brayan832015/Taller_Integrador/docs/final report/Figures/making/2_fabricacion_drilling.jpeg

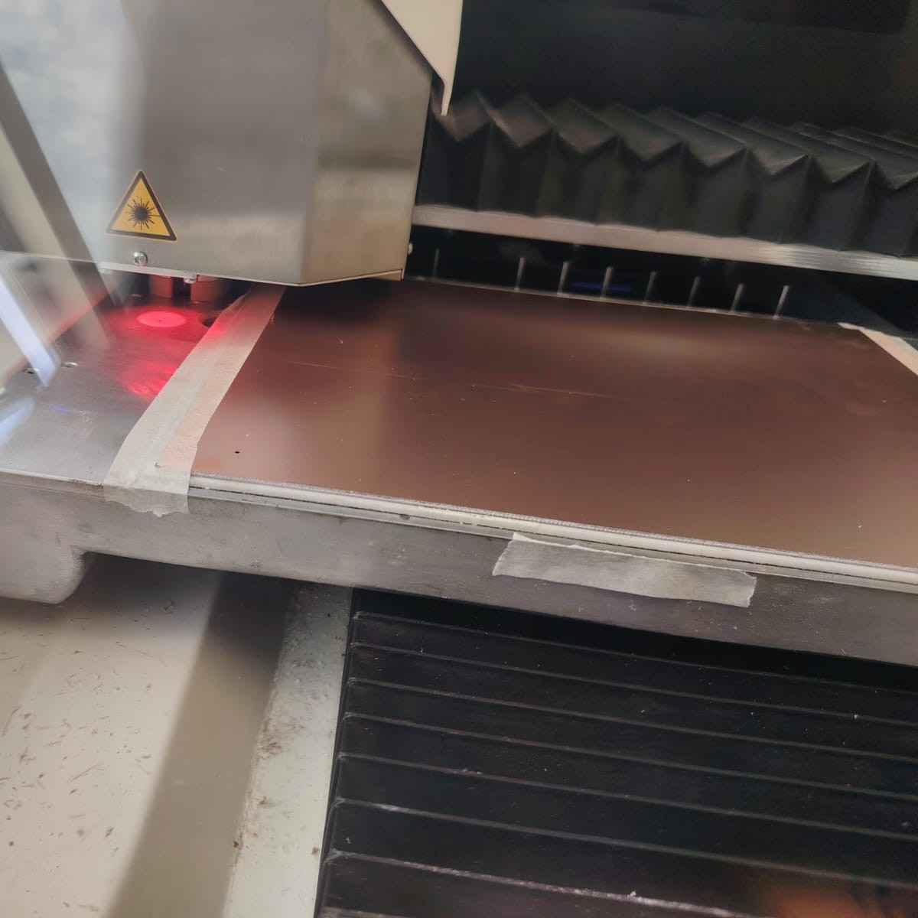
docs/final report/Figures/making/2_fabricacion_drilling.jpeg
