brayan832015/Taller_Integrador/docs/final report/Figures/making/4_fabricacion_baño.jpeg

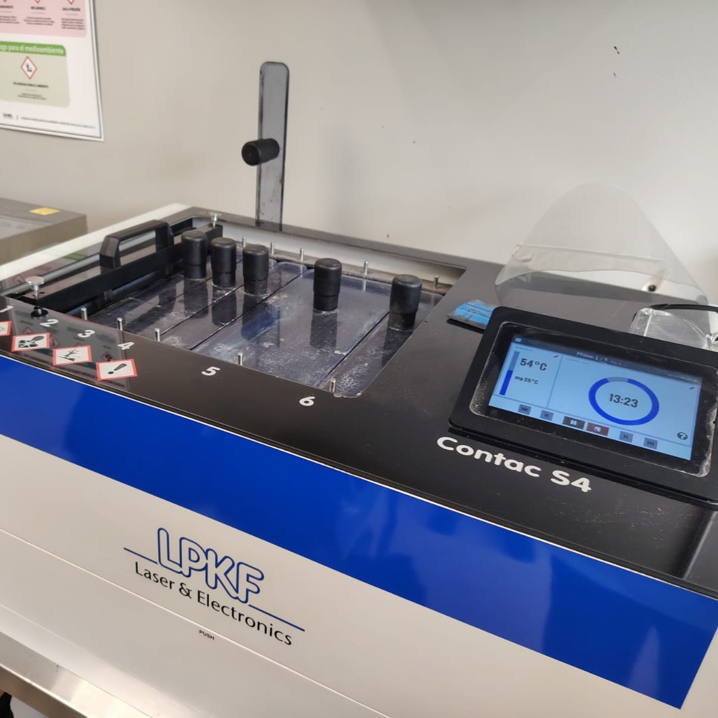
docs/final report/Figures/making/4_fabricacion_baño.jpeg
