brayan832015/Taller_Integrador/docs/final report/Figures/making/5_fabricacion_baño.jpeg

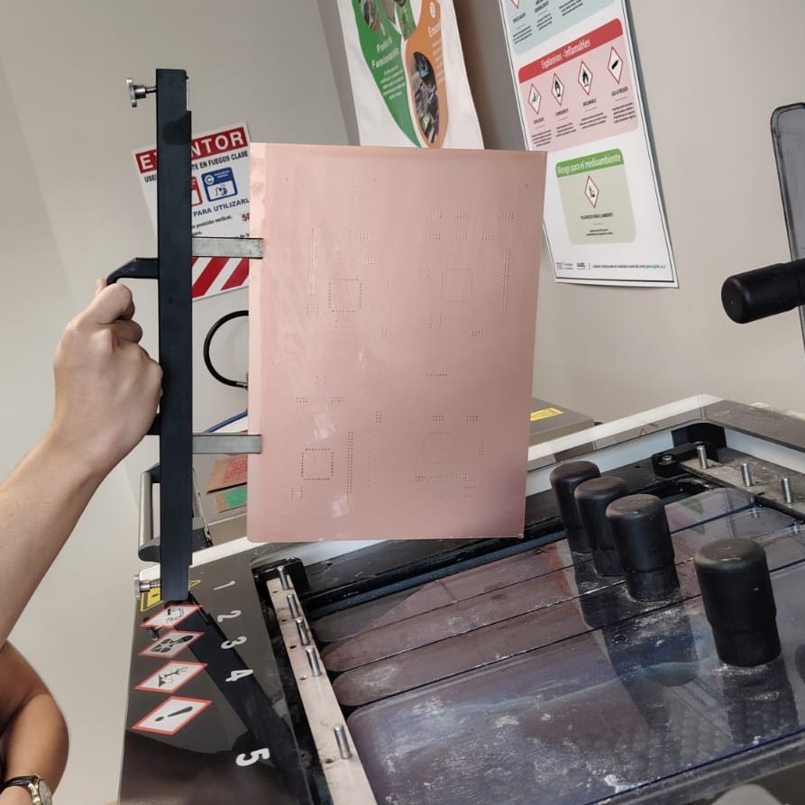
docs/final report/Figures/making/5_fabricacion_baño.jpeg
