brayan832015/Taller_Integrador/docs/final report/Figures/making/10_fabricacion_orificios_metal.jpeg

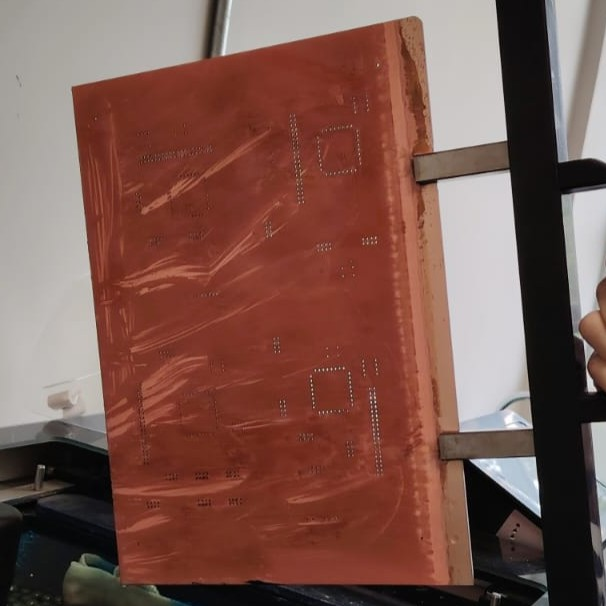
docs/final report/Figures/making/10_fabricacion_orificios_metal.jpeg
