brayan832015/Taller_Integrador/docs/final report/Figures/making/18_soldadura.jpeg

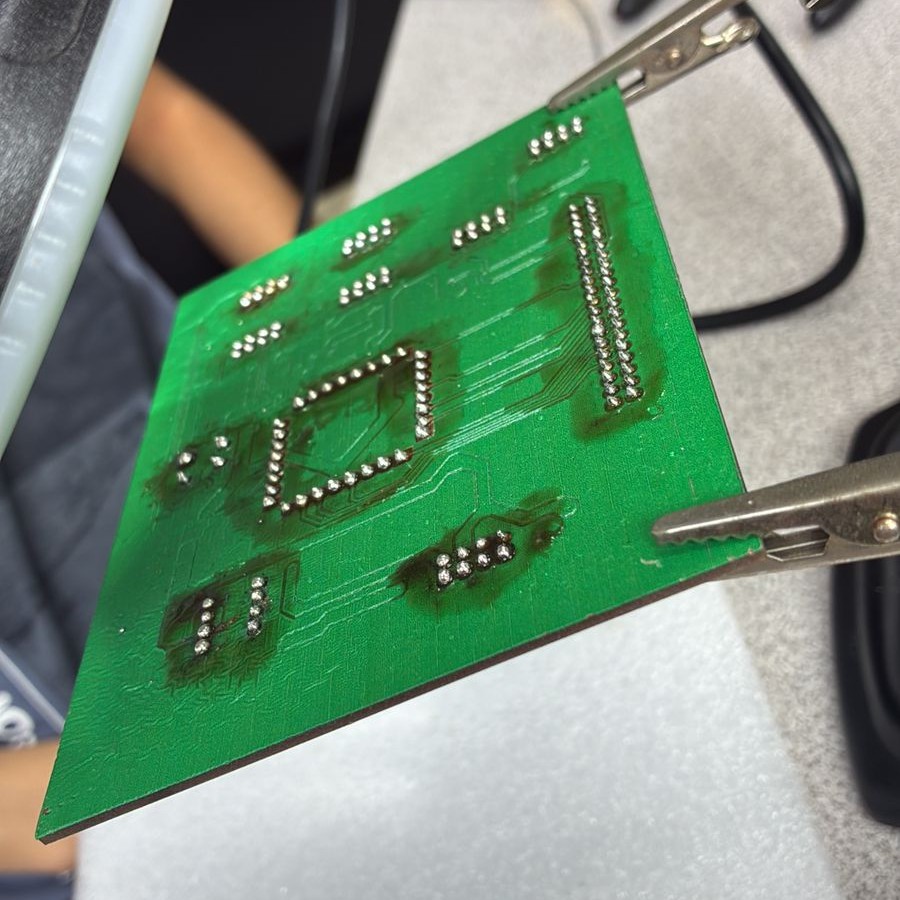
docs/final report/Figures/making/18_soldadura.jpeg
